dylangmiles/daisy-tone-trixter/audio/dsp_chain.h

// audio/dsp_chain.h — configurable, menu-ready DSP stage chain for Tone Trixter.
//
// Design goals (set 2026-06-07):
//   - Every effect is a Stage; every tunable is a Param (name/value/min/max/step).
//   - Stages run in series on the mono block, each independently enable/bypassable.
//   - A future encoder + OLED menu walks the SAME Param/Stage model that the UART
//     command interface drives today — so the control surface is swappable, not
//     rewritten.
//   - Param changes are real-time safe: a change marks the stage dirty and it
//     recomputes coefficients once at the next block boundary (never per-sample).
//
// Current chain order (post-IR; the IR itself is handled in es8388_test.cpp):
//   EQ (3-band) -> Dynamics (comp/limiter/sustain) -> Output level
//
// All control entry points are CORE 0 ONLY (called from the foreground loop that
// also runs dsp_chain_process). No cross-core access — no locks needed.
#ifndef TT_DSP_CHAIN_H
#define TT_DSP_CHAIN_H

#include <stdbool.h>
#include <stddef.h>

typedef struct {
    const char *name;     // short token used by the UART/menu (e.g. "mid_gain")
    float       value;
    float       vmin, vmax, vstep;
    const char *unit;     // "dB", "Hz", ":1", "ms", "x" — for menu display
} Param;

typedef struct Stage Stage;
struct Stage {
    const char *name;        // stage token (e.g. "eq", "comp", "out")
    bool        enabled;     // per-stage on/off (bypass when false)
    Param      *params;
    int         n_params;
    bool        dirty;       // params changed -> recompute() before next process()
    void      (*recompute)(Stage *self, float fs);
    void      (*process)(Stage *self, float *buf, int n);
    void       *state;       // stage-specific working state
};

// Global passthrough: when true, EQ + Dynamics are skipped (output level still
// applies, so levels stay safe). Per-stage `enabled` flags are preserved.
extern volatile bool g_dsp_bypass;

// Build the chain (EQ -> Dynamics -> Output) for the sample rate. out_level_lin
// seeds the output stage so it reproduces the legacy IR_OUTPUT_SCALE on boot.
void dsp_chain_init(float fs, float out_level_lin);

// Bypass make-up gain, 0..8, 1.0 = true unity. See byp_level in the Preset struct.
void  dsp_chain_set_byp_level(float g);
float dsp_chain_byp_level(void);

// Process one mono block of n samples in place through all enabled stages.
void dsp_chain_process(float *buf, int n);

// Effective IR state for the host loop: true only if the IR stage is enabled AND
// global bypass is off. The actual convolution runs cross-core in es8388_test.cpp.
bool dsp_chain_ir_enabled(void);

// Set the IR (convolution) stage enable directly. The host calls this from its IR
// selection logic — convolution is off when the "none" IR is selected.
void dsp_chain_set_ir_enabled(bool on);

// Peak compressor gain reduction in dB (<= 0) since the last call; resets each call.
// For a live "GR meter" while dialing the comp threshold. 0 dB = not compressing.
float dsp_chain_comp_gr_db(void);

// Peak input level to the comp in dBFS since the last call; resets each call. Set
// comp.thresh relative to this to know where the stage actually engages.
float dsp_chain_comp_in_db(void);

// --- Presets: named bundles of (IR ref + every stage's params/enables) ----------
// A preset is plain data so it can come from the built-in table OR be parsed from
// an SD card (see audio/tt_store) and installed at runtime. `ir` names the impulse
// response: a built-in name ("tanglewood"/"garrison") or a WAV filename on the card
// ("mycab.wav"); NULL/"" means "keep the current IR". The host (main.cpp) resolves
// the string to an actual convolver IR.
typedef struct {
    const char *name;
    const char *ir;                       // IR name/filename, or "none"/NULL = dry (no IR,
                                          // convolution off — the host selects the "none" IR)
    bool  in_on, eq_on, comp_on, out_on;
    float in_level;
    float lo_f, lo_g, mid_f, mid_g, mid_q, hi_f, hi_g;
    float thr, ratio, att, rel, mkup;
    float out_level;
    int   pga;                            // ES8388 input PGA gain in dB (0..24, 3 dB steps); <0 = leave PGA
                                          // unchanged on load. Passive K&K wants ~12; active Garrison ~6.
                                          // ⚠ IGNORED on the Daisy: the TAC5242 has no software gain.
    float byp_level;                      // ⚠ DAISY ADDITION (2026-09-07): gain applied ONLY in bypass,
                                          // 0..8. <=0 = unity. Exists so the A/B is LEVEL-MATCHED:
                                          // bypass is the raw input, while an engaged preset can be
                                          // ~+10 dB louder (tanglewood-slide's compressor alone makes
                                          // up 16 dB). A loudness difference invalidates an ear A/B --
                                          // louder just reads as "better" -- so this lifts the DRY
                                          // path to meet the wet one instead of turning the preset down.
                                          // ⚠ SET IT TO 1.0 (or omit) FOR ANY MEASUREMENT. It is a
                                          // listening aid; with it engaged a "bypass" reading is no
                                          // longer the front end alone.
    float bk_level;                       // ⚠ DAISY ADDITION (2026-09-06): backing-track level, 0..2.
                                          // <0 = leave the current level alone. Parsed from "bk.level"
                                          // in presets.txt. The Pico's parser ignores the key, so the
                                          // SD card stays readable by both pedals -- but this struct and
                                          // tt_store.cpp have now DIVERGED from the RP2350 copies. Port
                                          // the same change back if the two are to stay identical.
    float dry_mix;                        // ⚠ DAISY ADDITION (2026-09-25): high-passed DRY piezo blended
                                          // back onto the wet IR, 0..1, from "ir.dry". <0 = leave unchanged.
                                          // The body IR kills the piezo quack AND the pick-on-string clack
                                          // with it; a little dry (HP'd ~2.5 kHz so the quack stays out)
                                          // returns the pick attack. 0 = pure IR. Only acts when an IR is
                                          // loaded (blended in main.cpp's callback, not a dsp_chain stage).
} Preset;

int         dsp_chain_preset_count(void);
const char *dsp_chain_preset_name(int idx);
const char *dsp_chain_preset_ir(int idx);              // IR ref for preset idx ("" if none)
int         dsp_chain_preset_pga(int idx);            // ES8388 PGA dB for preset idx (<0 = leave unchanged)
int         dsp_chain_find_preset(const char *name);   // -1 if not found
// Apply preset idx (sets every stage's params + enables, marks them dirty).
// Returns 0 on success, -1 on bad index. The host reads dsp_chain_preset_ir(idx)
// to switch the convolver IR.
int         dsp_chain_load_preset(int idx);

// Replace the active preset list (e.g. parsed from the SD card). `arr` must remain
// valid for the program's life (static storage). n<=0 restores the built-in table.
void          dsp_chain_install_presets(const Preset *arr, int n);
// The built-in "default" preset — a seed for partially-specified SD presets.
const Preset *dsp_chain_default_preset(void);

// Number of stages / accessor — for the future menu to iterate generically.
int    dsp_chain_stage_count(void);
Stage *dsp_chain_stage(int i);

// Parse + apply one command line (Core 0). Returns true if recognised. Emits a
// short reply via printf. Recognised forms:
//   "<stage>.<param> <value>"   set a parameter (clamped to [min,max])
//   "<stage> on" | "<stage> off"  enable / bypass a stage
//   "bypass on" | "bypass off"  global EQ+Dynamics passthrough
//   "dump"                       print every stage + param
//   "help"                       print usage
bool dsp_chain_command(const char *line);

#endif // TT_DSP_CHAIN_H
