dylangmiles/daisy-tone-trixter/pcb/tools/gen_place.py

#!/usr/bin/env python3
"""gen_place.py -- first-pass placement + functional clustering on tone_trixter.kicad_pcb.

Run with KiCad's bundled python (pcbnew) AFTER 'Update PCB from Schematic', with KiCad CLOSED:
  /Applications/KiCad/KiCad.app/Contents/Frameworks/Python.framework/Versions/Current/bin/python3 \
      tools/gen_place.py [board.kicad_pcb]

Two stages:
 1. ANCHORS -- parts whose position is FIXED by the enclosure (OLED, encoder, LEDs, rear jacks,
    footswitch/battery/bond connectors, Seed, SD) + the three OPAs + Ch-B jack, placed per the
    mock-up and on the correct side (jacks + Seed on the BACK, hang below the board).
 2. CLUSTERING -- every remaining passive is assigned to the device it shares the most SIGNAL nets
    with (power/ground rails excluded) and gridded next to it: front-end A around U1, front-end B
    around U2, output around U3, Seed decoupling around U4, power section near the DC entry.

⚠ FIRST PASS -- anchor X-Y are mock-up defaults; verify sides/rotations in 3D. Re-run any time
(idempotent by reference). Tune clusters by hand after; this just gets them onto the board by group.
"""
import sys, os
from collections import defaultdict
import pcbnew

HERE = os.path.dirname(os.path.abspath(__file__))
BOARD = sys.argv[1] if len(sys.argv) > 1 else os.path.join(HERE, "..", "tone_trixter.kicad_pcb")

OX, OY = 30.0, 30.0        # board origin on the sheet (matches gen_board.py)
BW, BD = 132.0, 57.0

# anchor: ref -> (x, y, rot, side)  board-local mm; side F=top, B=bottom(hangs below).
# ⚠ The enclosure anchors are CAPTURED FROM THE BOARD (the builder's hand-placement, 2026-10-10) so
# re-running preserves it. The OPAs + Ch-B are placed by us (they were still in staging).
ANCHORS = {
    "J6":  (58.9, 48.0,  90, "F"),   # OLED header     (builder)
    "SW1": (36.5, 36.5,   0, "F"),   # encoder         (builder)
    "D4":  (4.7, 39.5,    0, "F"),   # LED             (builder)
    "D5":  (125.0, 39.0,  0, "F"),   # LED             (builder)
    "J1":  (20.0, 43.5, 180, "B"),   # IN  jack K3599  (builder)
    "J2":  (112.0, 43.5, 180, "B"),  # OUT jack K3599  (builder)
    "J8":  (46.0, 43.5, 180, "B"),   # IN B jack K3599 (second high-Z input, drilled v1 -- beside IN A)
    "J3":  (127.5, 27.0, 180, "B"),  # DC  lead        (builder)
    "J7":  (50.5, 3.0,  180, "B"),   # bypass sw lead  (builder)
    "J9":  (93.5, 3.0,  180, "B"),   # tuner sw lead   (builder)
    "J4":  (127.5, 17.5,180, "B"),   # battery lead    (builder)
    "J5":  (7.0, 12.5,  180, "B"),   # enclosure bond  (builder)
    "U4":  (95.0, 26.5,  90, "B"),   # Daisy Seed3     (builder)
    "J10": (111.7, 8.9,   0, "B"),   # microSD         (builder)
    # --- active devices placed by us (near their function; drag as needed) ---
    "U1":  (66.0, 11.0,   0, "F"),   # OPA front-end A
    "U2":  (66.0, 20.0,   0, "F"),   # OPA front-end B
    "U3":  (66.0, 29.0,   0, "F"),   # OPA output stage
}

# Passive clusters grid in the OPEN CENTRE (between the left controls and the right Seed), grouped
# by function, so they land on the board without colliding with the builder's edge placement. Drag
# each group to its final home afterwards. (grid top-left, board-local)
CLUSTER_ORIGIN = {
    "U1":   (48.0, 8.0),    # front-end A passives
    "U2":   (48.0, 18.0),   # front-end B passives
    "U3":   (48.0, 28.0),   # output passives
    "U4":   (48.0, 38.0),   # Seed decoupling + SD resistors
    "PWR":  (76.0, 8.0),    # power section
    "MISC": (76.0, 22.0),   # unassigned (film caps, star, TPs) -- sort by hand
}

def mm(x): return pcbnew.FromMM(x)
def at(x, y): return pcbnew.VECTOR2I(mm(OX + x), mm(OY + y))

def is_rail(n):
    return (not n) or n.startswith("+") or "GND" in n or n.startswith("unconnected") \
        or n in ("VIN", "VREF", "VBUS", "VCC")

def main():
    board = pcbnew.LoadBoard(BOARD)
    fps = {f.GetReference(): f for f in board.GetFootprints()}

    def set_side_pos(f, x, y, rot, side):
        if (side == "B") != f.IsFlipped():
            f.Flip(f.GetPosition(), False)
        f.SetPosition(at(x, y)); f.SetOrientationDegrees(rot)

    # --- stage 1: anchors ---
    for ref, (x, y, rot, side) in ANCHORS.items():
        if ref in fps: set_side_pos(fps[ref], x, y, rot, side)

    # signal-net sets per footprint
    sig = {r: {p.GetNetname() for p in f.Pads() if not is_rail(p.GetNetname())}
           for r, f in fps.items()}
    rails = {r: {p.GetNetname() for p in f.Pads() if is_rail(p.GetNetname())}
             for r, f in fps.items()}

    HUBS = ("U1", "U2", "U3")   # the signal hubs that attract passives
    clusters = defaultdict(list)
    for ref, f in fps.items():
        if ref in ANCHORS:
            continue
        # best signal hub
        best, score = None, 0
        for h in HUBS:
            s = len(sig[ref] & sig[h])
            if s > score: best, score = h, s
        # also let the Seed attract its direct-signal passives
        s_u4 = len(sig[ref] & sig["U4"])
        if s_u4 > score: best, score = "U4", s_u4
        if best is None:
            # rail-only part: route by dominant rail
            rs = rails[ref]
            if any("+9" in n or n == "VIN" for n in rs):      best = "PWR"
            elif any("+3V3D" in n for n in rs):               best = "U4"
            elif any("+3V3A" in n or "VREF" in n for n in rs): best = "U1"
            else:                                             best = "MISC"
        clusters["U4" if best == "U4" else best].append(ref)

    # --- stage 2: grid each cluster near its origin ---
    placed = 0
    for key, refs in clusters.items():
        ox, oy = CLUSTER_ORIGIN.get(key, CLUSTER_ORIGIN["MISC"])
        refs.sort(key=lambda r: (r[0], int("".join(c for c in r if c.isdigit()) or 0)))
        cols, pitch = 5, 3.4
        for i, ref in enumerate(refs):
            f = fps[ref]
            if f.IsFlipped(): f.Flip(f.GetPosition(), False)
            f.SetPosition(at(ox + (i % cols) * pitch, oy + (i // cols) * pitch))
            f.SetOrientationDegrees(0)
            placed += 1

    pcbnew.SaveBoard(BOARD, board)
    print(f"anchors+hubs placed: {sum(1 for r in ANCHORS if r in fps)}")
    for k in sorted(clusters):
        print(f"  cluster {k:5}: {len(clusters[k])} parts -> {' '.join(clusters[k])}")
    print(f"clustered {placed} passives")

if __name__ == "__main__":
    try:
        main()
    except Exception as e:
        print("ERROR:", e, file=sys.stderr); raise
